MohamadAminGhanoum/Custom-devboard/assets/Difficulty in pcb.png

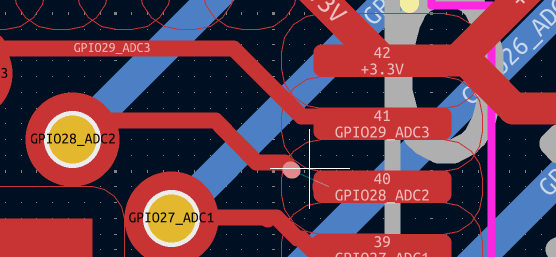
assets/Difficulty in pcb.png
