MohamadAminGhanoum/Custom-devboard/assets/Errors i got.png

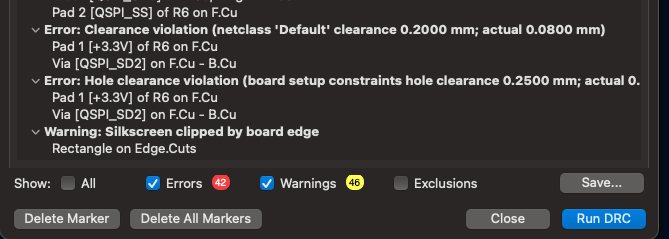
assets/Errors i got.png
