MohamadAminGhanoum/Custom-devboard/assets/Final PCB.png

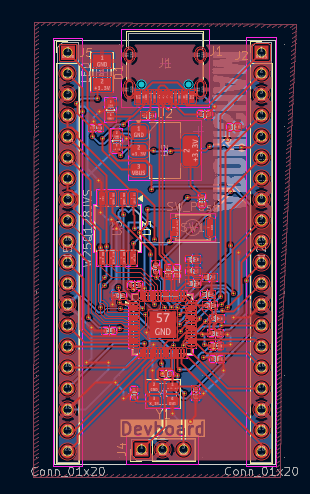
assets/Final PCB.png
