MohamadAminGhanoum/Custom-devboard/assets/Footprints.png

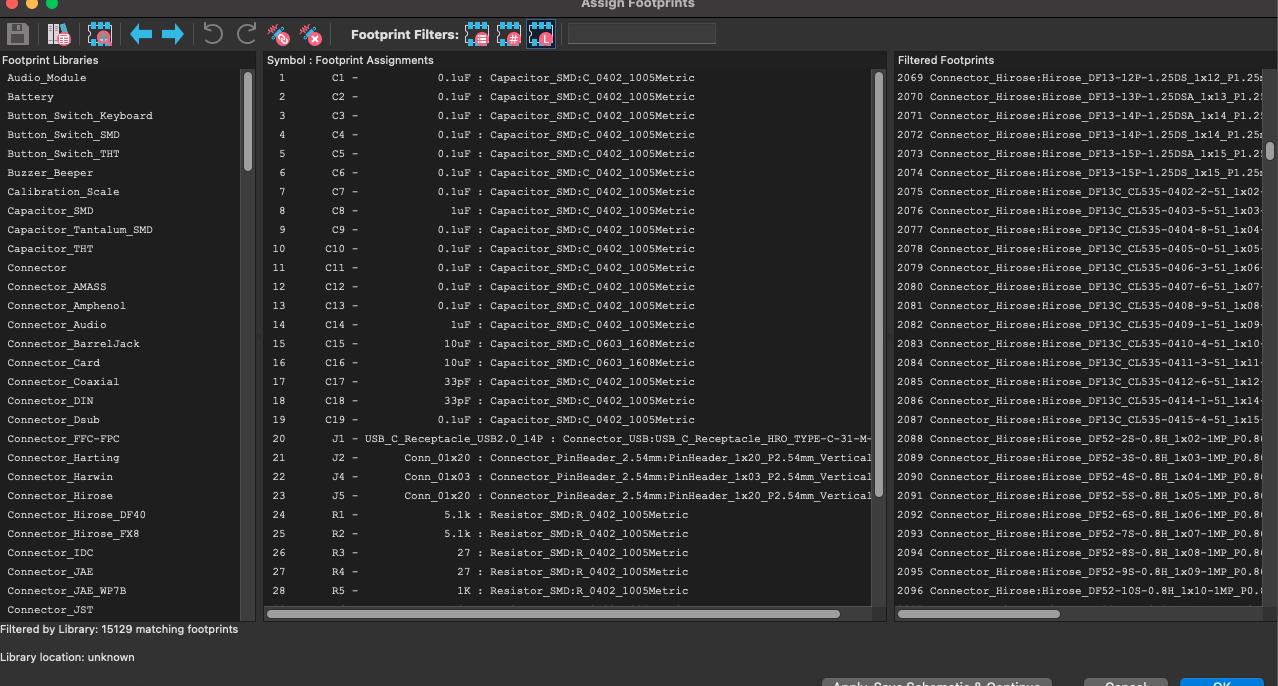
assets/Footprints.png
