MohamadAminGhanoum/Custom-devboard/assets/JLC PCB price.jpeg

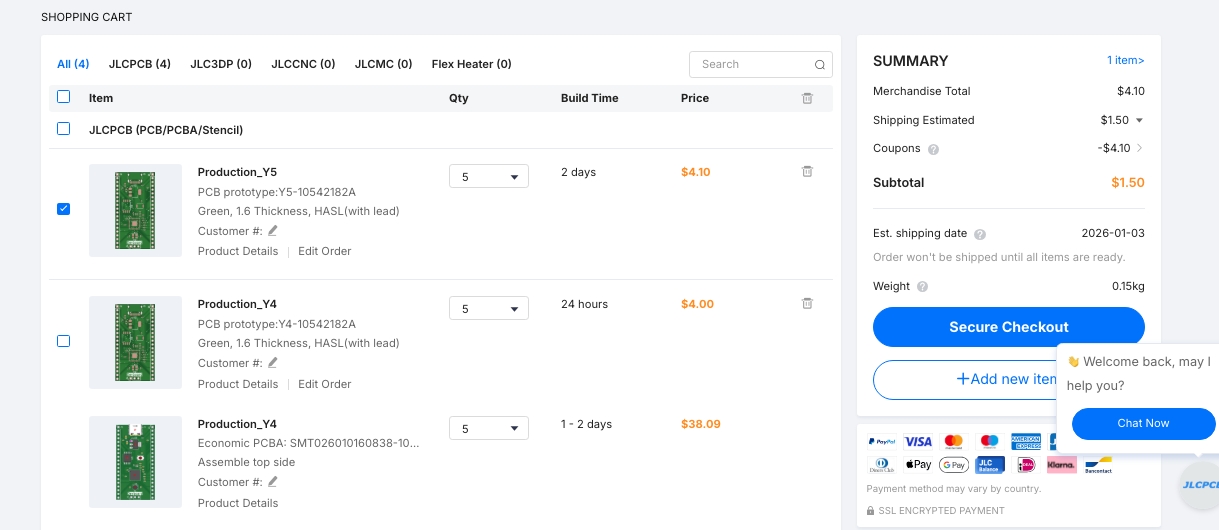
assets/JLC PCB price.jpeg
