MohamadAminGhanoum/Custom-devboard/assets/LCSC electronics - price.jpeg

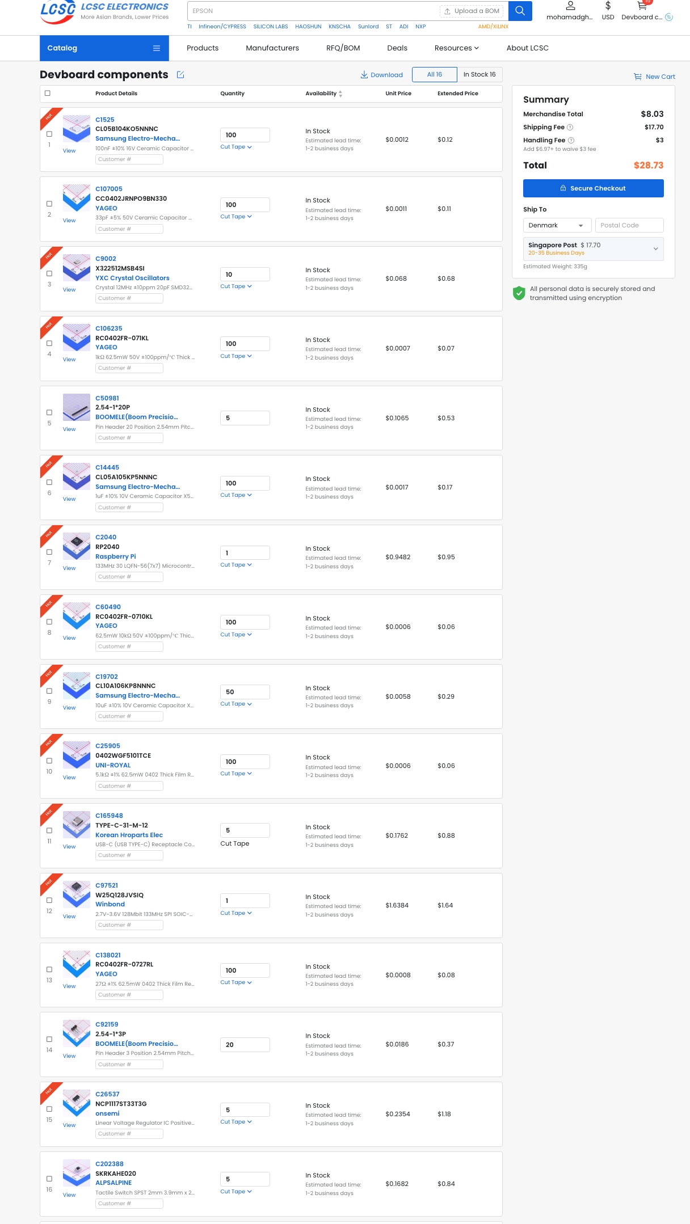
assets/LCSC electronics - price.jpeg
