MohamadAminGhanoum/Custom-devboard/assets/PCB.png

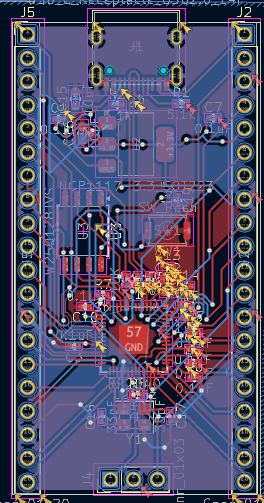
assets/PCB.png
