MohamadAminGhanoum/Custom-devboard/assets/schematic-1.png

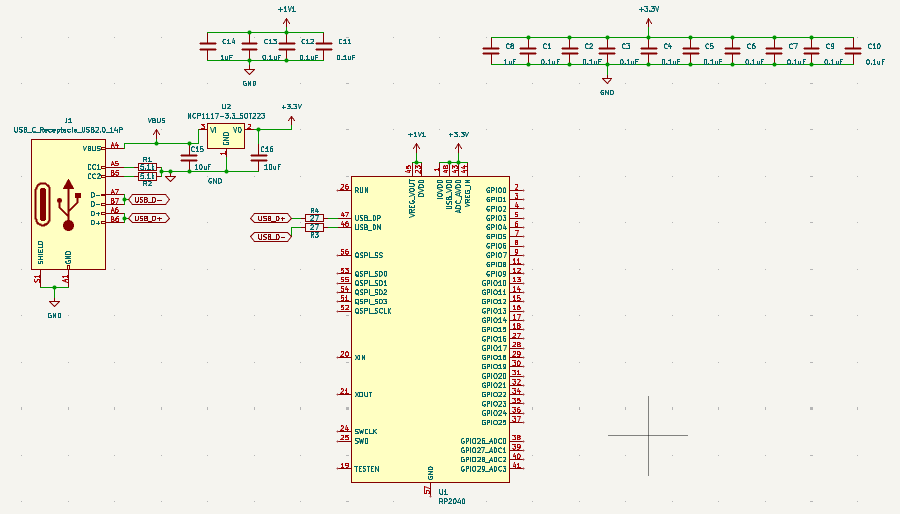
assets/schematic-1.png
