MohamadAminGhanoum/Custom-devboard/assets/schematic-2.png

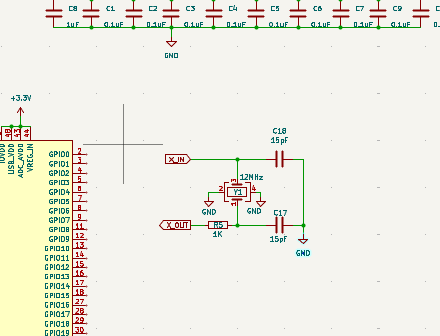
assets/schematic-2.png
