MohamadAminGhanoum/Custom-devboard/assets/Schematic-5.png

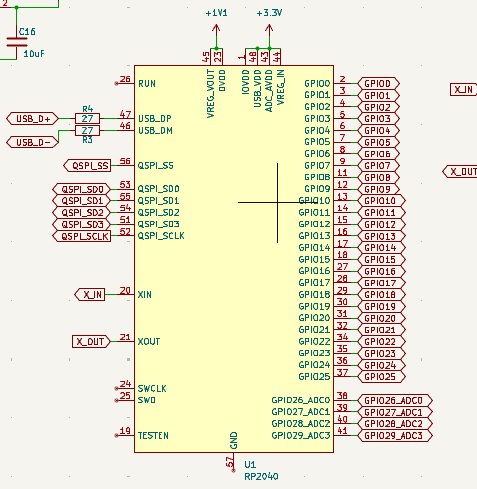
assets/Schematic-5.png
