MohamadAminGhanoum/Custom-devboard/assets/Schematic-6.png

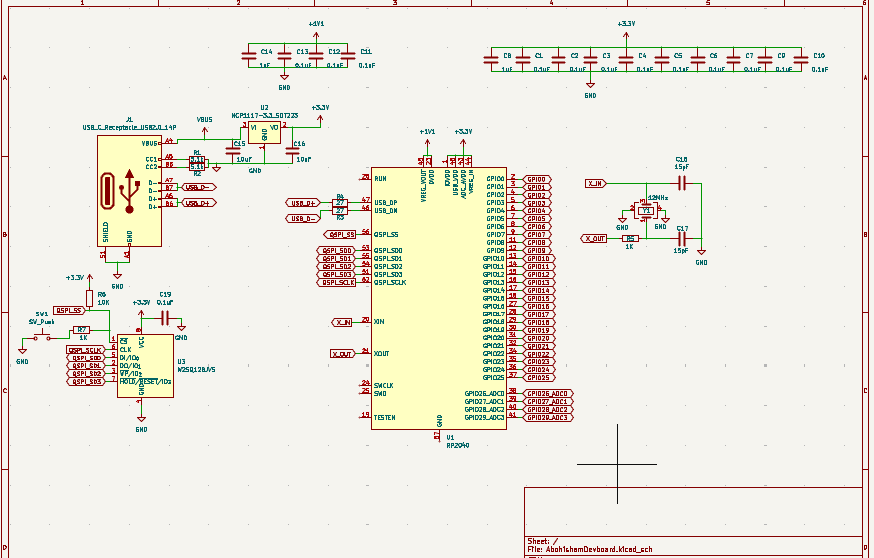
assets/Schematic-6.png
